libc0607/GI_Dice/dice/src/BLE_Dice/APP/include/peripheral.h

/********************************** (C) COPYRIGHT *******************************
 * File Name          : peripheral.h
 * Author             : WCH
 * Version            : V1.0
 * Date               : 2018/12/11
 * Description        :
 * Copyright (c) 2021 Nanjing Qinheng Microelectronics Co., Ltd.
 * SPDX-License-Identifier: Apache-2.0
 *******************************************************************************/

#ifndef PERIPHERAL_H
#define PERIPHERAL_H

#ifdef __cplusplus
extern "C" {
#endif

/*********************************************************************
 * INCLUDES
 */

/*********************************************************************
 * CONSTANTS
 */

// Peripheral Task Events
#define SBP_START_DEVICE_EVT    0x0001

#define SBP_READ_RSSI_EVT       0x0004
#define SBP_PARAM_UPDATE_EVT    0x0008
#define UART_TO_BLE_SEND_EVT    0x0010

/*********************************************************************
 * MACROS
 */
typedef struct
{
    uint16_t connHandle; // Connection handle of current connection
    uint16_t connInterval;
    uint16_t connSlaveLatency;
    uint16_t connTimeout;
} peripheralConnItem_t;

/*********************************************************************
 * FUNCTIONS
 */

/*
 * Task Initialization for the BLE Application
 */
extern void Peripheral_Init(void);

/*
 * Task Event Processor for the BLE Application
 */
extern uint16_t Peripheral_ProcessEvent(uint8_t task_id, uint16_t events);

void patch_mac_addr_to_ble_conf();

/*********************************************************************
*********************************************************************/

#ifdef __cplusplus
}
#endif

#endif
